mindflayer-vtt/mindflayer-keypad/include/HardwareConfig.h

#pragma once
#define HARDWARE_ID "mindflayer-keypad-v1"
#define NEOPIXEL_DATA_PIN 3
#define FIRMWARE_SIGNING_PUBLIC_KEY_PEM                                                            \
  "-----BEGIN PUBLIC KEY-----\n"                                                                   \
  "MIIBIjANBgkqhkiG9w0BAQEFAAOCAQ8AMIIBCgKCAQEA2ehVgtICR8BmvoxzTsRt\n"                             \
  "CXcULVGcYVx5loUIG81MJTYPwE3EEReeK4K4sTnA/EADduSB/G4eWK0XwD70ulBr\n"                             \
  "CUUvbNqJ5bwlfCThoO6BQU6nacZBDGUIjC0d6ZbcsXRTLa7u4w6OdyUSFfYlzTL2\n"                             \
  "UAzTOeFV8BDGif4jIWeKD8/Bdff4c5dH0AigZPyLuHJMHRvs6tLrwnUU8vpC+WQ0\n"                             \
  "EFU4dAYtwGeSmSQg6yEvOgJ8jrOIxuQhNiuXhgMlLrFjsbvTEHXcPnaCzDM1svWl\n"                             \
  "8K2iPiC7858TYspUPNqyb7NCm5L6jY63v20mhxLX/P4jj45pY3+Xfq9aU9NnhQgN\n"                             \
  "mwIDAQAB\n"                                                                                     \
  "-----END PUBLIC KEY-----\n"
