mindflayer-vtt/mindflayer-keypad/test/host/application_deadline.cpp

// Execute the real application orchestrator with simulated SDK time and I/O.
#include <Application.h>
#include <ApplicationState.h>
#include <BootControl.h>
#include <DebugLog.h>
#include <KeyboardMatrix.h>
#include <LedController.h>
#include <NeoPixelBus.h>
#include <ProvisioningStorage.h>
#include <cassert>
#include <cstdio>
extern "C" {
#include <user_interface.h>
}

bool wifiConnected = true, publicKeyValid = true;
namespace {
namespace KeyboardMatrix = com::viromania::vtt::wss::KeyboardMatrix;
uint32_t now = 0;
os_timer_t* sdkTimer = nullptr;
bool temporary = true, stored = true;
bool testStatusLeds = false;
bool recoveryMode = false;
unsigned recoveryChecks = 0, serialPolls = 0, deviceBegins = 0;
uint32_t connectDelay = 0, pollDelay = 0;
ApplicationState state;
struct Restart {};
void expectLed(unsigned index, unsigned r, unsigned g, unsigned b) {
  assert(testLedPixels[index].R == r);
  assert(testLedPixels[index].G == g);
  assert(testLedPixels[index].B == b);
}
KeyboardMatrix::KeyState matrix[4][3] = {
    {{"Q"}, {"W"}, {"E"}},
    {{"A"}, {"S"}, {"D"}},
    {{"Z"}, {"X"}, {"C"}},
    {{"SHI"}, {""}, {"SPC"}},
};
} // namespace

extern "C" {
void os_timer_disarm(os_timer_t* timer) { timer->armed = false; }
void os_timer_setfn(os_timer_t* timer, os_timer_func_t* callback, void* argument) {
  timer->callback = callback;
  timer->argument = argument;
}
void os_timer_arm(os_timer_t* timer, uint32_t milliseconds, bool repeat) {
  assert(!repeat);
  timer->deadline = now + milliseconds;
  timer->armed = true;
  sdkTimer = timer;
}
void system_restart() { throw Restart{}; }
}
unsigned long millis() { return now; }
void delay(unsigned long milliseconds) {
  if (!wifiConnected && testLedBegins)
    expectLed(0, 255, 0, 0);
  if (sdkTimer && sdkTimer->armed && milliseconds >= uint32_t(sdkTimer->deadline - now)) {
    now = sdkTimer->deadline;
    sdkTimer->armed = false;
    sdkTimer->callback(sdkTimer->argument);
  }
  now += milliseconds;
  // Keep the broken pre-fix startup loop from hanging the regression runner.
  if (now > 120000)
    throw "rollback did not occur";
}
void FakeEsp::restart() { system_restart(); }
ApplicationState& applicationState() { return state; }
void printHeapStats() {}
namespace BootControl {
bool begin() { return true; }
bool isTemporaryBoot() { return temporary; }
uint8_t currentSlot() { return temporary ? 1 : 0; }
uint8_t permanentSlot() { return 0; }
} // namespace BootControl
namespace mindflayer::provisioning {
bool loadStored(Provisioning&, Selection* selection) {
  *selection = {COPY_A, 1};
  return stored;
}
} // namespace mindflayer::provisioning
namespace DebugLog {
void setEnabled(bool) {}
bool isEnabled() { return false; }
void print(const char*) {}
void println(const char*) {}
void flush() {}
} // namespace DebugLog
namespace FirmwareUpdate {
void installSignatureVerifier() {}
} // namespace FirmwareUpdate
namespace SerialProvisioning {
void configureSerial() {}
void clearRecoveryMarker() {}
bool enterRecoveryModeIfRequested(bool isTemporary) {
  ++recoveryChecks;
  return recoveryMode && !isTemporary;
}
void poll() { ++serialPolls; }
} // namespace SerialProvisioning
namespace com::viromania::vtt::wss::KeyboardMatrix {
KeyState::KeyState(const char* name) : isDown(false) {
  std::strncpy(key, name, 3);
  key[3] = 0;
}
void initMatrix() {}
KeyState (*getState())[4][3] { return &matrix; }
} // namespace com::viromania::vtt::wss::KeyboardMatrix
namespace DeviceConnection {
void begin() {
  ++deviceBegins;
  if (testStatusLeds)
    expectLed(0, 255, 255, 0);
  delay(connectDelay);
}
void poll() { delay(pollDelay); }
} // namespace DeviceConnection
namespace RBootTestHooks {
void maybeFailBeforeServerAcknowledgement(bool, uint32_t) {}
} // namespace RBootTestHooks

int main(int argc, char** argv) {
  assert(argc == 2);
  const std::string scenario = argv[1];
  if (scenario == "unprovisioned-pulse") {
    temporary = stored = false;
    Application::setup();
    assert(!state.provisioned && !state.serialProvisioningMode);
    assert(recoveryChecks == 1 && testLedBegins == 1);
    const uint32_t started = now;
    // Three complete cycles: rise for 500 ms, fall for 500 ms, dark for 2 s.
    for (uint32_t cycle = 0; cycle < 3; ++cycle) {
      for (uint32_t phase : {0u, 250u, 500u, 750u, 1000u, 2000u, 2990u}) {
        now = started + cycle * 3000 + phase;
        Application::loop();
        const unsigned red = phase == 500 ? 255 : (phase == 250 || phase == 750) ? 127 : 0;
        expectLed(0, red, 0, 0);
        expectLed(1, red, 0, 0);
      }
    }
    const unsigned shows = testLedShows;
    Application::loop();
    assert(testLedShows == shows); // Do not retransmit an unchanged dark frame.
    assert(serialPolls == 0 && testWifiBegins == 0 && deviceBegins == 0);
    std::puts("unprovisioned pulse regression passed");
    return 0;
  }
  if (scenario == "status-leds") {
    temporary = false;
    testStatusLeds = true;
    // Serial recovery must not initialize DMA, with or without stored settings.
    LedController::showConnectionStatus(false, false);
    assert(testLedBegins == 0 && testLedShows == 0);
    stored = false;
    recoveryMode = true;
    Application::setup();
    Application::loop();
    assert(testLedBegins == 0 && testLedShows == 0);
    assert(state.serialProvisioningMode && serialPolls == 1);
    stored = true;
    recoveryMode = true;
    Application::setup();
    Application::loop();
    assert(testLedBegins == 0 && testLedShows == 0);
    assert(state.serialProvisioningMode && serialPolls == 2);
    delete state.serverPublicKey;
    state.serverPublicKey = nullptr;
    recoveryMode = false;
    Application::setup();
    assert(testLedBegins == 1);
    assert(testLedShows == 2);
    assert(testFirstShown[0].R == 255 && testFirstShown[0].G == 0 && testFirstShown[0].B == 0);
    expectLed(0, 255, 255, 0);
    expectLed(1, 0, 0, 0);
    state.wssHealthy = true; // TLS alone must not show green.
    Application::loop();
    expectLed(0, 255, 255, 0);
    state.authenticated = true;
    Application::loop();
    expectLed(0, 0, 255, 0);
    LedController::setColors(10, 20, 30, 40, 50, 60);
    const unsigned shows = testLedShows;
    Application::loop();
    assert(testLedShows == shows); // Do not overwrite server colors each loop.
    expectLed(0, 10, 20, 30);
    state.client.connected = false;
    Application::loop();
    expectLed(0, 255, 255, 0);
    expectLed(1, 40, 50, 60);
    wifiConnected = false;
    Application::loop();
    expectLed(0, 255, 0, 0);
    assert(!state.wifiHealthy);
    wifiConnected = true;
    state.authenticated = false;
    state.client.connected = true;
    Application::loop();
    expectLed(0, 255, 255, 0);
    state.authenticated = true;
    Application::loop();
    expectLed(0, 0, 255, 0);
    expectLed(1, 40, 50, 60);
    delete state.serverPublicKey;
    std::puts("connection status LED regression passed");
    return 0;
  }
  if (scenario == "restart-shortcut") {
    temporary = false;
    // Exercise the real application loop for every combination of all 12 matrix
    // positions, including the unused position and the old Q-based shortcut.
    for (unsigned mask = 0; mask < 4096; ++mask) {
      for (unsigned index = 0; index < 12; ++index)
        matrix[index / 3][index % 3].isDown = (mask & (1u << index)) != 0;
      const unsigned chord = (1u << 2) | (1u << 9) | (1u << 11);
      for (bool provisioned : {false, true}) {
        state.provisioned = provisioned;
        bool restarted = false;
        try {
          Application::loop();
        } catch (const Restart&) {
          restarted = true;
        }
        assert(restarted == (provisioned && (mask & chord) == chord));
      }
    }
    std::puts("restart shortcut regression passed");
    return 0;
  }
  if (scenario == "wifi-unavailable")
    wifiConnected = false;
  else if (scenario == "provisioning-failure")
    stored = false;
  else if (scenario == "invalid-public-key")
    publicKeyValid = false;
  else if (scenario == "blocked-connect")
    connectDelay = 100000;
  else if (scenario == "blocked-poll")
    pollDelay = 100000;
  else if (scenario == "permanent")
    temporary = false;
  else
    assert(false);
  bool restarted = false;
  try {
    Application::setup();
    while (now < 120000) {
      Application::loop();
      delay(10);
    }
  } catch (const Restart&) {
    restarted = true;
  } catch (const char* message) {
    std::fprintf(stderr, "%s\n", message);
  }
  delete state.serverPublicKey;
  assert(restarted == temporary);
  if (temporary)
    assert(now == 90000);
  else
    assert(!sdkTimer || !sdkTimer->armed);
  std::puts("application deadline regression passed");
}
