mindflayer-vtt/mindflayer-keypad/test/host/Arduino.h

#pragma once

#include <cstdint>
#include <cstring>
#include <string>

using String = std::string;
using byte = uint8_t;
constexpr int LOW = 0, HIGH = 1, INPUT_PULLUP = 2, OUTPUT = 1;
void pinMode(uint8_t pin, int mode);
void digitalWrite(uint8_t pin, int value);
int digitalRead(uint8_t pin);
unsigned long millis();
void delay(unsigned long milliseconds);
void optimistic_yield(uint32_t);

struct FakeSerial {
  template <typename... Args> void printf(const char*, Args...) {}
};
inline FakeSerial Serial;
struct FakeEsp {
  unsigned long getFlashChipRealSize() { return 0x400000; }
  unsigned long getFlashChipSize() { return 0x400000; }
  void restart();
};
inline FakeEsp ESP;
